Ck-coder-boop/Accelerometer-highest-score-game/Game module sheet.kicad_sch

## KiCad design Game module sheet.kicad_sch (2026-05-04)

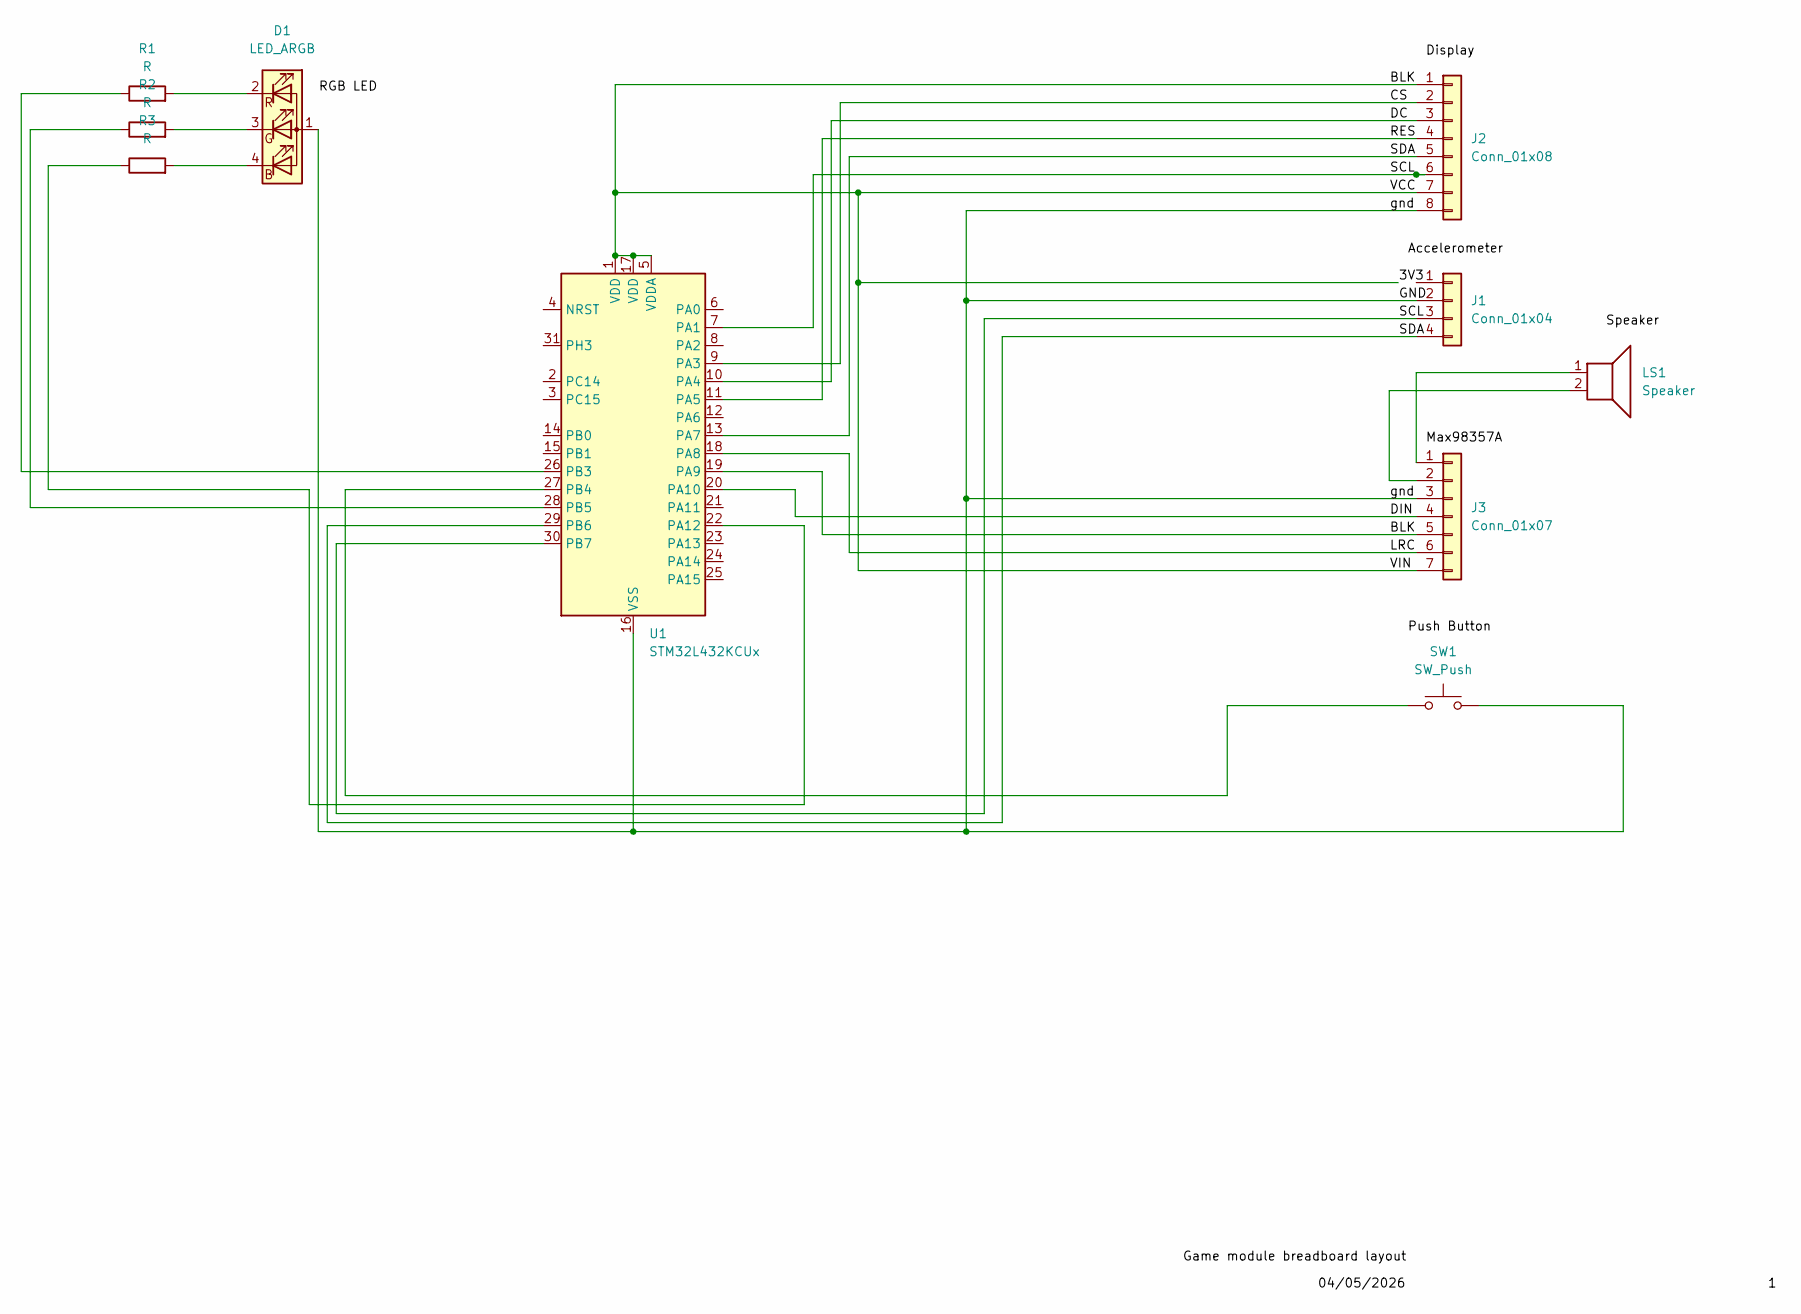
[picture p5: schematic Game module sheet.kicad_sch]

Parts:
D1: LED_ARGB
J1: Conn_01x04
J2: Conn_01x08
J3: Conn_01x07
LS1: Speaker
R1, R2, R3: R
SW1: SW_Push
U1: STM32L432KCUx; QFN-32-1EP_5x5mm_P0.5mm_EP3.45x3.45mm

Connections:
3V3: J2.1, J2.7, J3.5, J3.7, U1.1 (VDD), U1.5 (VDDA), U1.17 (VDD), U1.19 (PA9)
CS: J2.2, U1.9 (PA3)
DC: J2.3, U1.10 (PA4)
DIN: J3.4, U1.20 (PA10)
LRC: J3.6, U1.18 (PA8)
unnamed: D1.2 (RK), R1.2
unnamed: D1.3 (GK), R2.2
unnamed: D1.4 (BK), R3.2
unnamed: J3.1, LS1.1
unnamed: J3.2, LS1.2
unnamed: R1.1, U1.26 (PB3)
unnamed: R2.1, U1.28 (PB5)
unnamed: R3.1, U1.22 (PA12)
unnamed: SW1.1, U1.27 (PB4)
RES: J2.4, U1.11 (PA5)
SCL: J1.3, J2.6, U1.7 (PA1), U1.30 (PB7)
SDA: J1.4, J2.5, U1.13 (PA7), U1.29 (PB6)
gnd: D1.1 (A), J1.2, J2.8, J3.3, SW1.2, U1.16 (VSS), U1.32 (VSS), U1.33 (VSS)
