Ck-coder-boop/Accelerometer-highest-score-game/sound_array.h

#ifndef SOUND_ARRAY_H
#define SOUND_ARRAY_H

#include <stdint.h>

const int16_t sound_data[] = {
3,2,-1,-5,5,-1,3,0,4,-5,
-1,-4,0,-3,4,-1,-3,4,7,0,
-4,-2,1,2,4,7,3,-11,-4,5,
2,2,9,-7,-7,-3,0,0,-8,-5,
0,4,0,4,0,3,-5,-1,-2,-2,
5,0,1,-1,3,-5,-6,-4,6,21,
1,1,6,-6,1,-8,1,-3,-1,-8,
-11,-7,-15,-4,-6,9,-5,-5,3,-8,
5,1,12,8,-12,-10,1,-6,-15,3,
-8,-5,7,-9,10,11,-26,-30,-1030,-1108,
-1834,-1484,-1405,-226,1609,3118,4135,4658,4017,1463,
-1099,-3460,-5161,-5579,-3891,-868,1701,4468,5750,5052,
2765,51,-2960,-5127,-5223,-3766,-1146,1779,4338,4836,
3743,1736,-1147,-3591,-4563,-3616,-1961,550,3259,4318,
3974,2420,446,-2206,-3683,-3845,-3040,-1505,593,2125,
2486,2536,1876,658,-335,-573,-588,-736,-266,-395,
-1071,-1831,-1919,-1868,-1155,757,2461,3645,4047,3648,
1437,-1285,-3483,-5234,-5451,-3897,-900,1878,4487,5794,
4988,2625,-240,-2973,-5288,-5176,-3526,-1045,1714,4021,
4716,3376,1412,-1297,-3735,-4752,-3916,-1953,586,3552,
4898,4646,2822,414,-2591,-4527,-4632,-3760,-1837,725,
2990,3625,3336,2391,563,-916,-1627,-1519,-1362,-415,
232,151,-305,-746,-1145,-1343,-203,1204,2288,2937,
3019,1700,-621,-2536,-4182,-4827,-3856,-1352,1361,3775,
5419,5009,2971,65,-2617,-4825,-5141,-3591,-1231,1606,
4139,5250,4103,1902,-810,-3544,-4986,-4491,-2418,171,
3241,5237,5285,3721,1198,-1932,-4599,-5333,-4644,-2804,
22,2766,4180,4147,3370,1394,-773,-2253,-2581,-2432,
-1495,-179,447,538,425,180,-356,-176,553,1300,
2039,2390,1787,62,-1561,-2954,-3918,-3520,-1690,552,
2419,4092,4260,2731,413,-1937,-3975,-4679,-3508,-1508,
1010,3322,4618,3932,1971,-481,-3124,-4720,-4520,-2579,
-130,2837,5052,5353,4024,1529,-1503,-4463,-5646,-5071,
-3327,-553,2290,4322,4611,3910,2024,-493,-2310,-3126,
-3043,-2265,-641,585,1091,1234,1008,320,-147,158,
518,981,1355,1208,241,-962,-1918,-2744,-2602,-1319,
562,2293,3559,3816,2470,578,-1494,-3302,-4256,-3370,
-1484,795,2748,4044,3779,1792,-648,-2950,-4538,-4286,
-2771,-96,2895,5143,5745,3871,1252,-1828,-5184,-6235,
-5548,-3320,-77,3208,5686,5847,4431,1756,-1292,-3966,
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
};

const unsigned int sound_length = sizeof(sound_data) / sizeof(sound_data[0]);

#endif
